L3B-ER-974/L3B_ER_projet_2025/Schémas_typon/Gerber/Schéma_Gerber_Jean.pdf

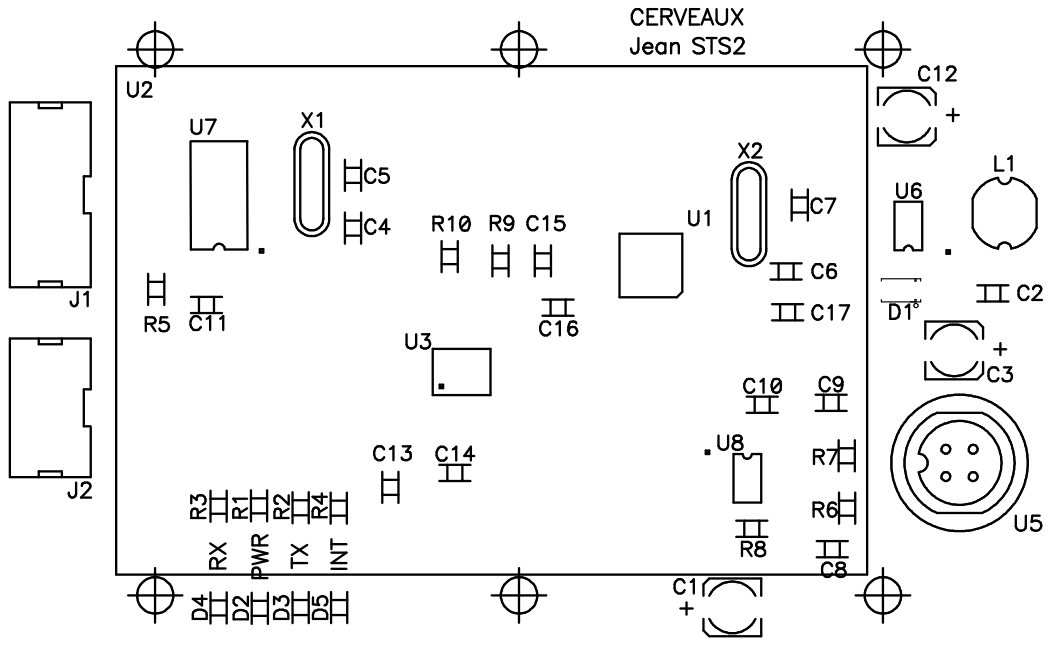
[picture p8: page 4]

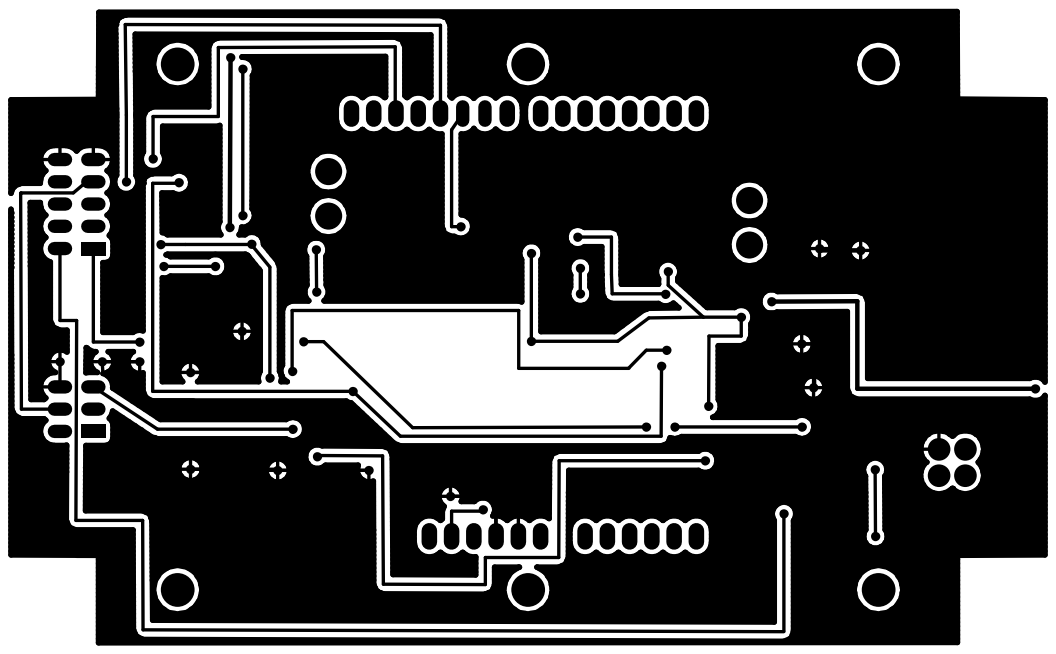
[picture p9: page 5]

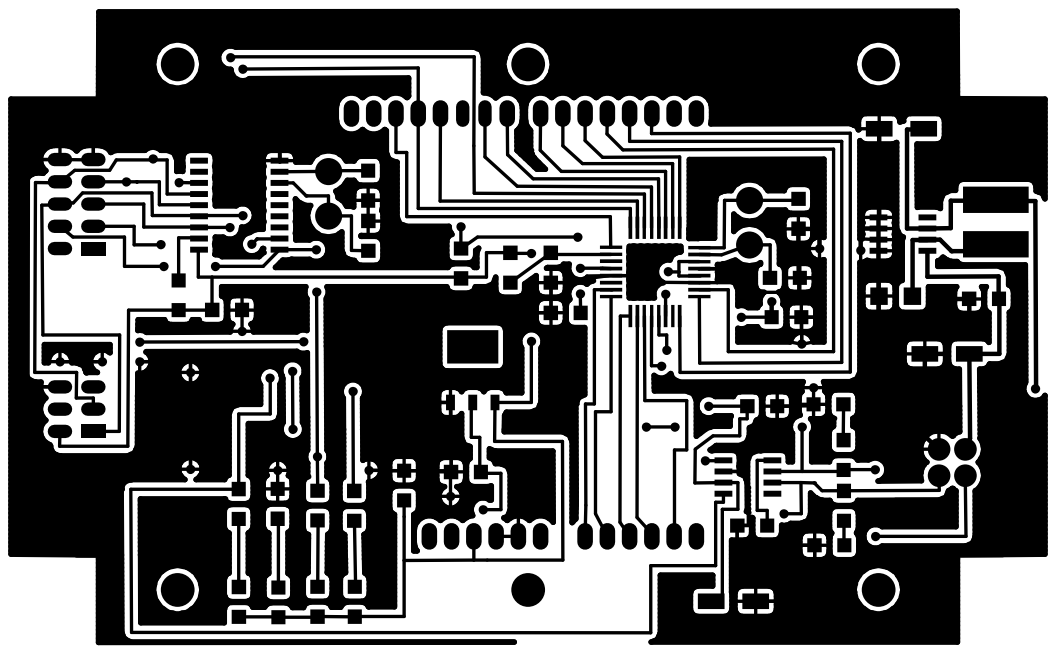
[picture p10: page 6]
